angelazhang8/GuideMouse/Processing-code/t-marble.jpg

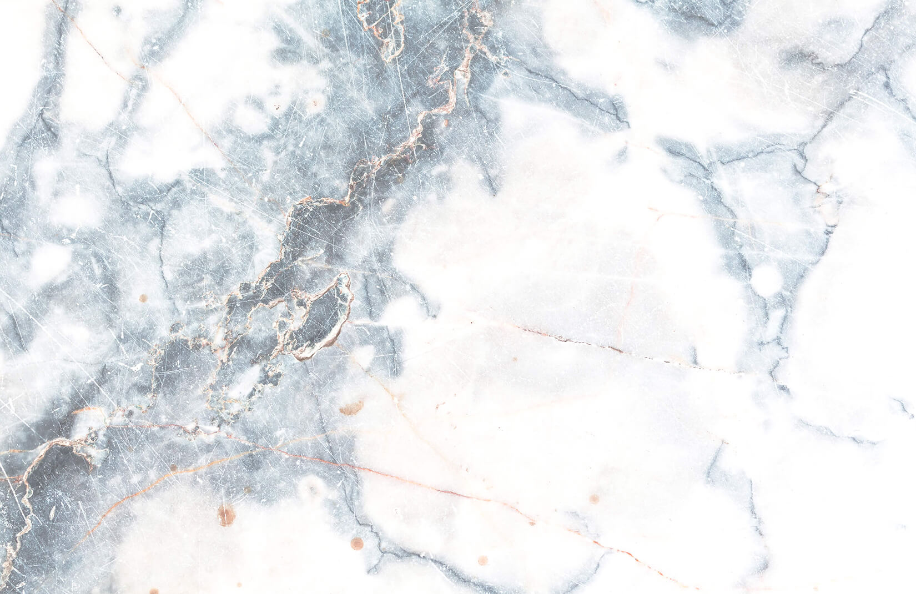
Processing-code/t-marble.jpg
