angelazhang8/GuideMouse/AutoCAD-models/STL files/middle-peg-holder.stl

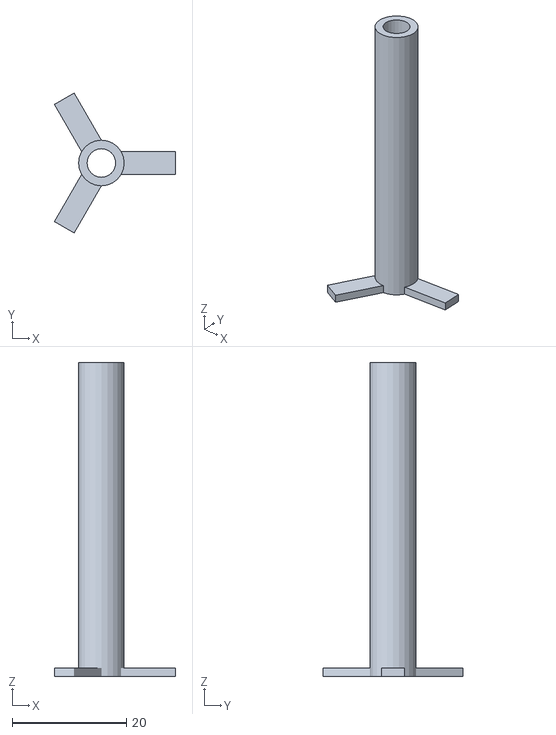
[picture p24: CAD file, 2020-02-18]
AutoCAD-models/STL files/middle-peg-holder.stl
21.2 x 24.5 x 55.0
