angelazhang8/GuideMouse/Processing-code/s-rat.obj

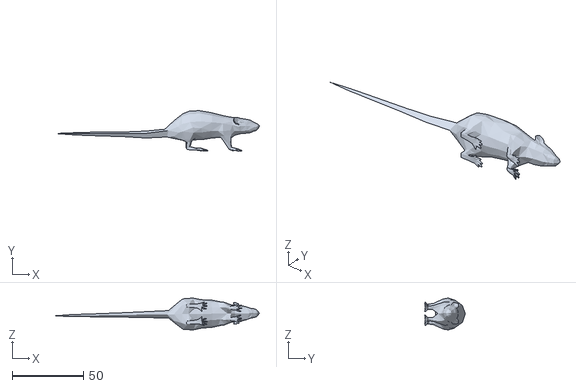
[picture p25: CAD file, 2020-02-18]
Processing-code/s-rat.obj
144.3 x 28.6 x 22.5
