angelazhang8/GuideMouse/Processing-code/s-tree.obj

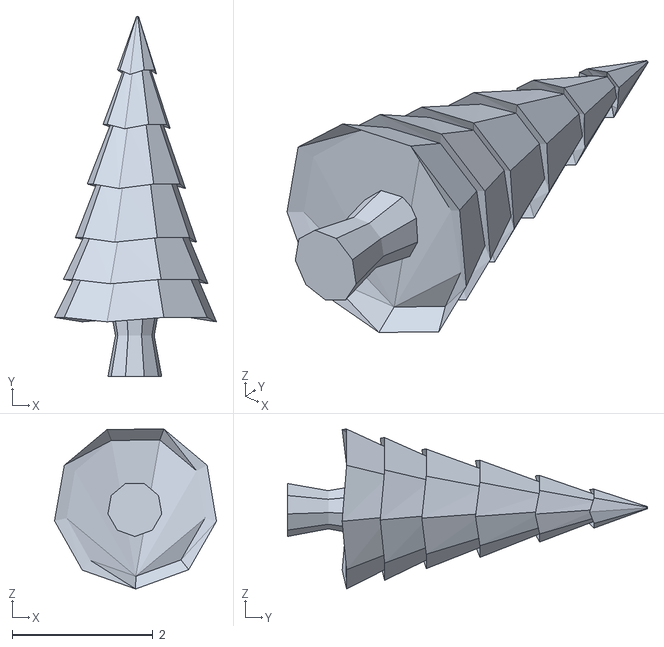
[picture p26: CAD file, 2020-02-18]
Processing-code/s-tree.obj
2.31 x 5.12 x 2.28
