angelazhang8/GuideMouse/Processing-code/s-deer.obj

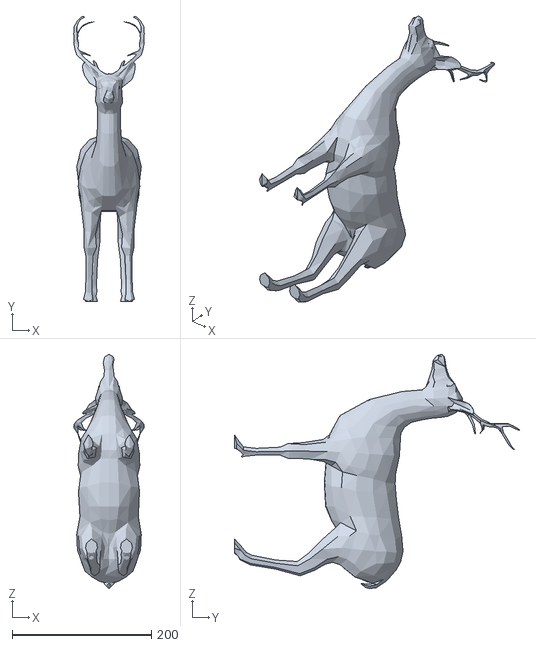
[picture p27: CAD file, 2020-02-18]
Processing-code/s-deer.obj
101.4 x 409.5 x 336.3
