angelazhang8/GuideMouse/Processing-code/s-goat.obj

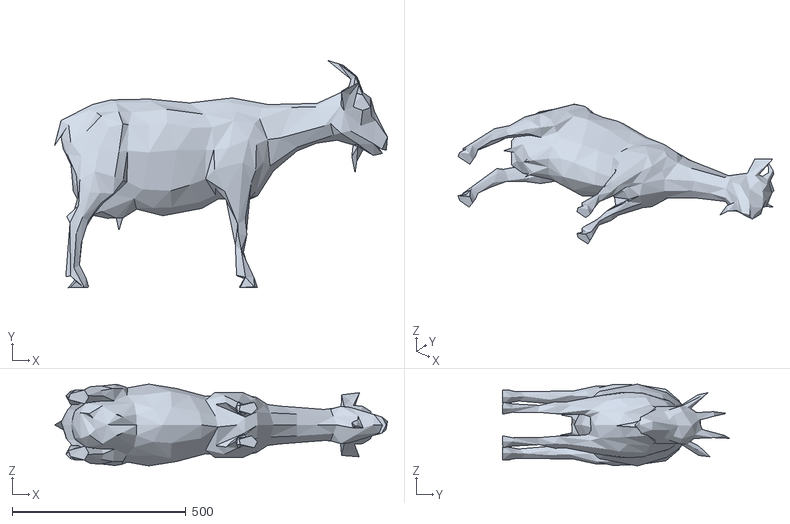
[picture p28: CAD file, 2020-02-18]
Processing-code/s-goat.obj
957.9 x 654.3 x 235.4
