angelazhang8/GuideMouse/Processing-code/s-angel.obj

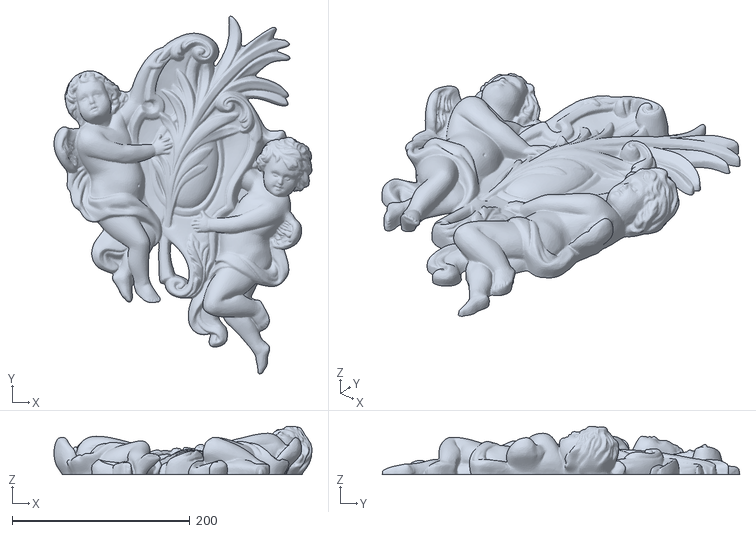
[picture p29: CAD file, 2020-02-18]
Processing-code/s-angel.obj
290.4 x 402.8 x 54.2
