angelazhang8/GuideMouse/Processing-code/s-cow.obj

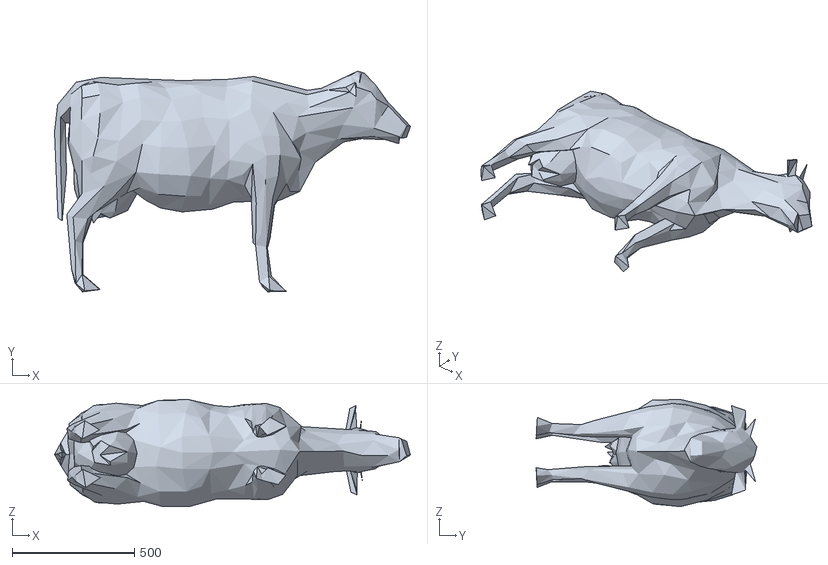
[picture p30: CAD file, 2020-02-18]
Processing-code/s-cow.obj
1456.0 x 902.8 x 438.3
