angelazhang8/GuideMouse/AutoCAD-models/PDFs/Rack and Pinion/Rack.pdf

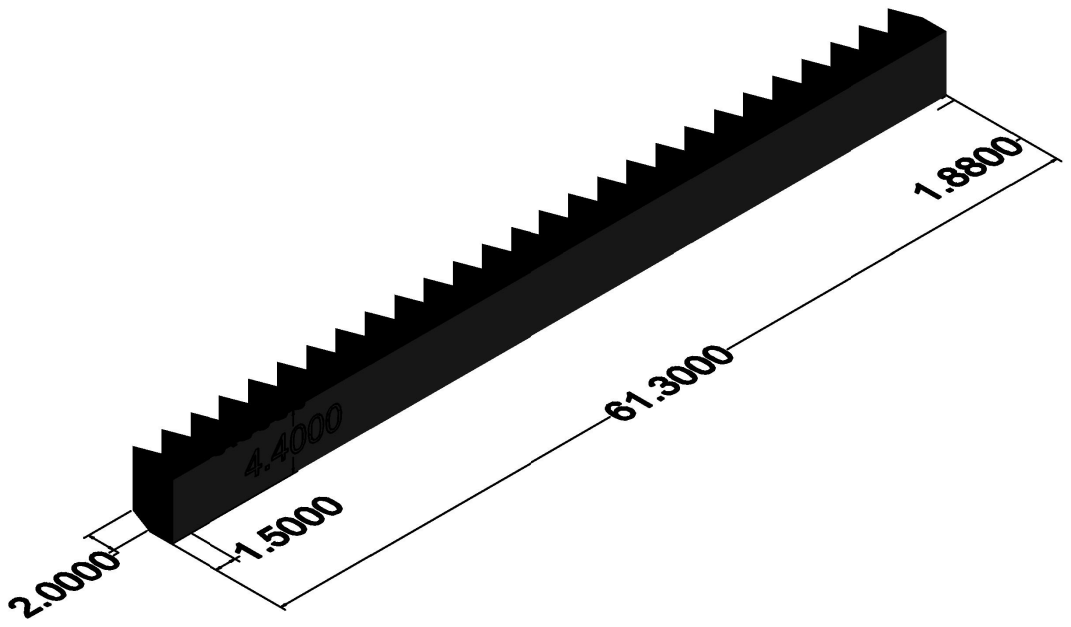
[picture p52: page 1]
