angelazhang8/GuideMouse/AutoCAD-models/PDFs/Rack and Pinion/RackNonSolid.pdf

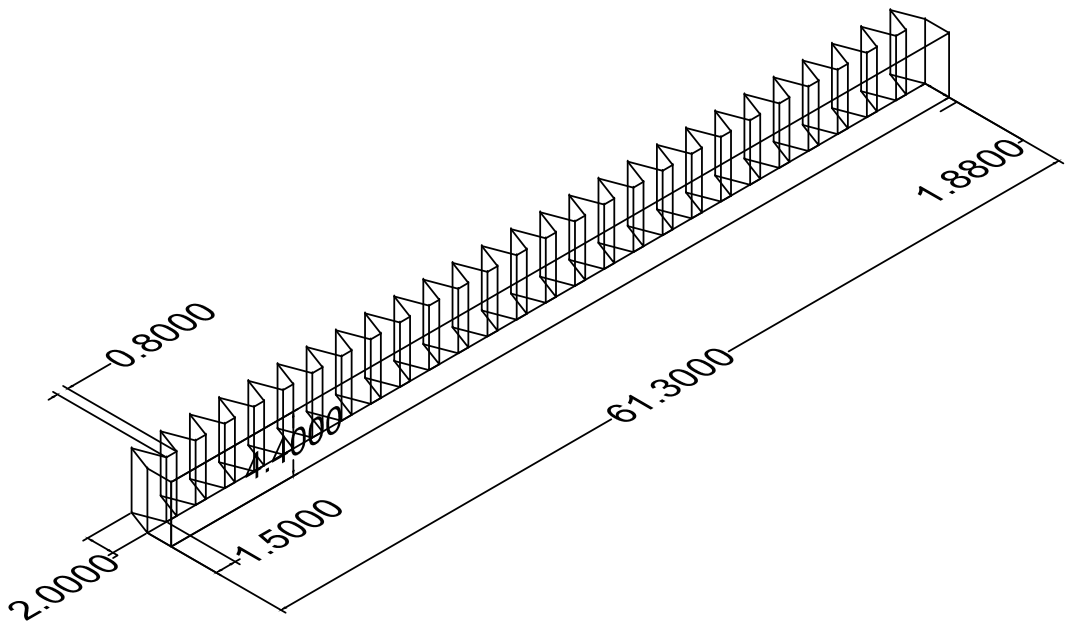
[picture p53: page 1]
