angelazhang8/GuideMouse/AutoCAD-models/PDFs/Rack and Pinion/RackOtherOtherSide.pdf

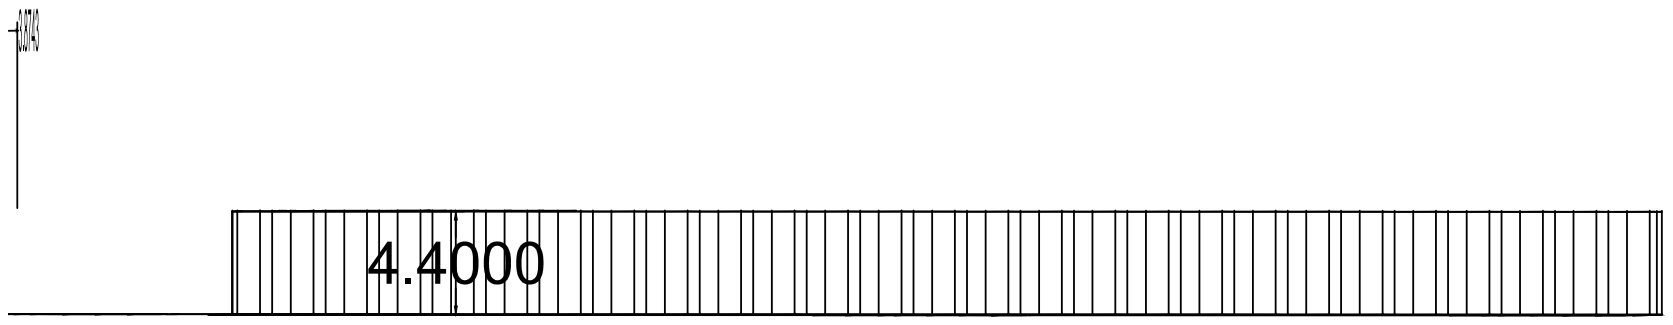
[picture p54: page 1]
