angelazhang8/GuideMouse/AutoCAD-models/PDFs/Rack and Pinion/RackOtherSide.pdf

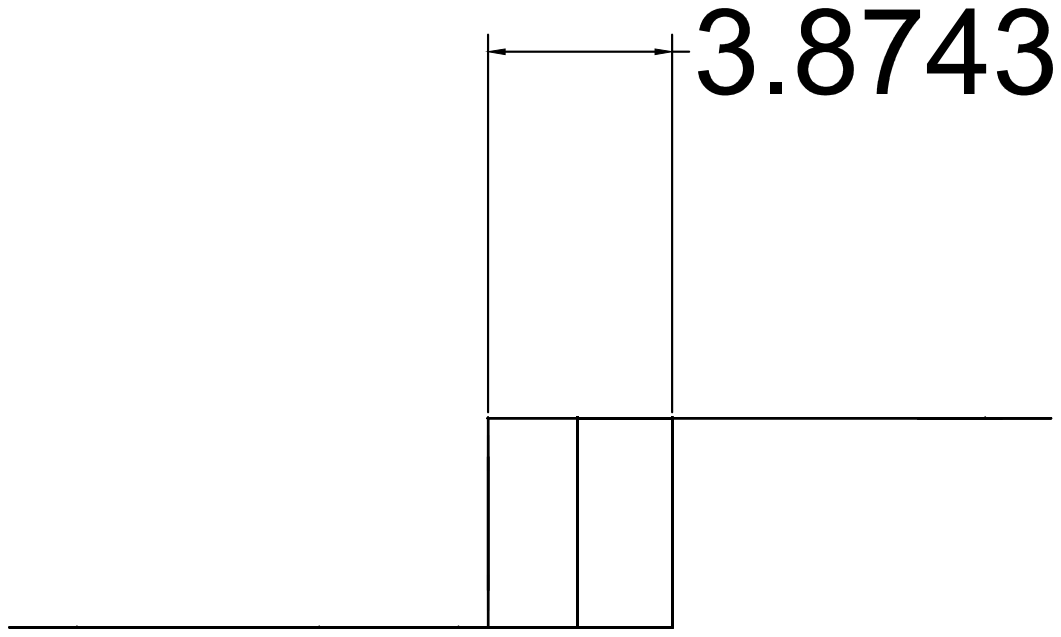
[picture p55: page 1]
