angelazhang8/GuideMouse/AutoCAD-models/PDFs/Rack and Pinion/RackSide.pdf

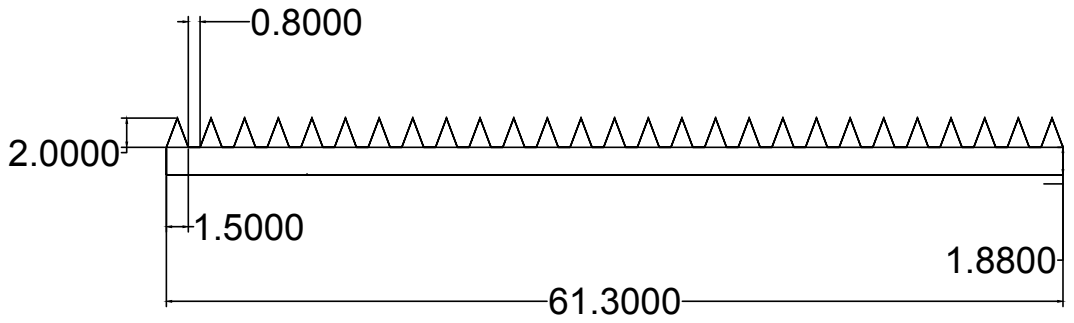
[picture p56: page 1]
